misterobotique/ZTH11-Zigbee-Temperature-Humidity-Sensor/Schematic/ZTH11-ZTU_V1.2.kicad_sch

## KiCad design Schematic/ZTH11-ZTU_V1.2.kicad_sch (2026-03-07)

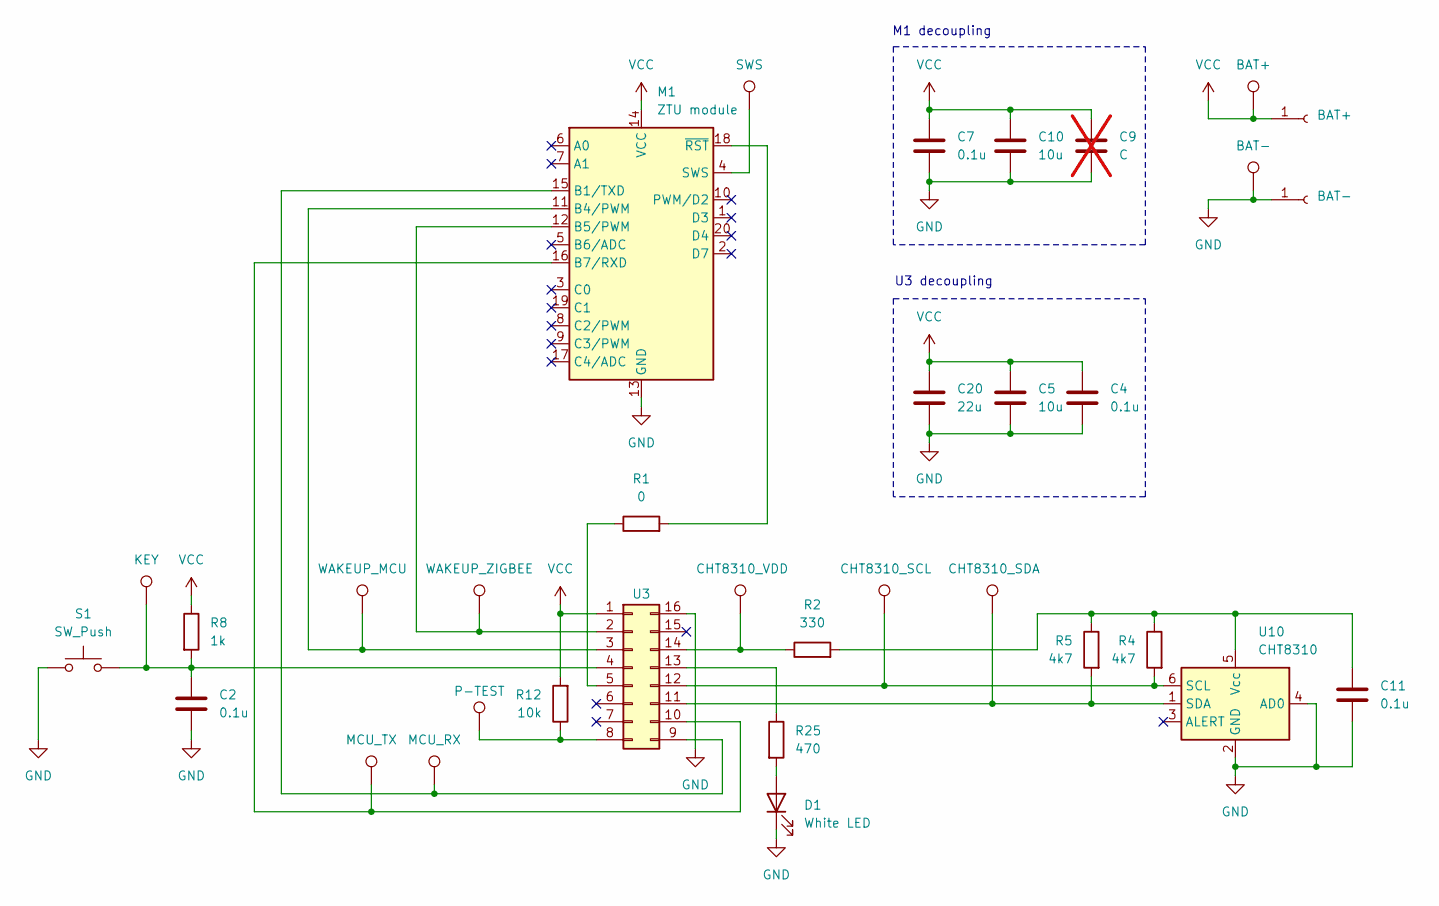
[picture p8: schematic ZTH11-ZTU_V1.2.kicad_sch]

Parts:
BAT+: TestPoint
BAT-: Conn_01x01_Socket
C2, C4, C7, C11: 0.1u
C5, C10: 10u
C9: C; not fitted
C20: 22u
CHT8310_SCL, CHT8310_SDA, CHT8310_VDD: TestPoint
D1: White LED
KEY: TestPoint
M1: ZTU module
MCU_RX: TestPoint
MCU_TX: TestPoint
P-TEST: TestPoint
R1: 0
R2: 330
R4, R5: 4k7
R8: 1k
R12: 10k
R25: 470
S1: SW_Push
SWS: TestPoint
U3: Conn_02x08_Counter_Clockwise
U10: CHT8310
WAKEUP_MCU: TestPoint
WAKEUP_ZIGBEE: TestPoint

Connections:
GND: BAT-.1, C2.2, C4.2, C5.2, C7.2, C9.2, C10.2, C11.2, C20.2, D1.1 (K), M1.13 (GND), S1.1, U3.16, U10.2 (GND), U10.4 (AD0)
unnamed: C2.1, KEY.1, R8.2, S1.2, U3.4
unnamed: C11.1, R2.2, R4.1, R5.1, U10.5 (Vcc)
unnamed: CHT8310_SCL.1, R4.2, U3.12, U10.6 (SCL)
unnamed: CHT8310_SDA.1, R5.2, U3.11, U10.1 (SDA)
unnamed: CHT8310_VDD.1, R2.1, U3.14
unnamed: D1.2 (A), R25.2
unnamed: M1.4 (SWS), SWS.1
unnamed: M1.11 (B4/PWM), U3.3, WAKEUP_MCU.1
unnamed: M1.12 (B5/PWM), U3.2, WAKEUP_ZIGBEE.1
unnamed: M1.15 (B1/TXD), MCU_RX.1, U3.9
unnamed: M1.16 (B7/RXD), MCU_TX.1, U3.10
unnamed: M1.18 (~RST), R1.2
unnamed: P-TEST.1, R12.1, U3.8
unnamed: R1.1, U3.5
unnamed: R25.1, U3.13
VCC: BAT+.1, C4.1, C5.1, C7.1, C9.1, C10.1, C20.1, M1.14 (VCC), R8.1, R12.2, U3.1

Notes on the sheet:
M1 decoupling
U3 decoupling
