misterobotique/ZTH11-Zigbee-Temperature-Humidity-Sensor/Measurements/data_sending(log_scale).png

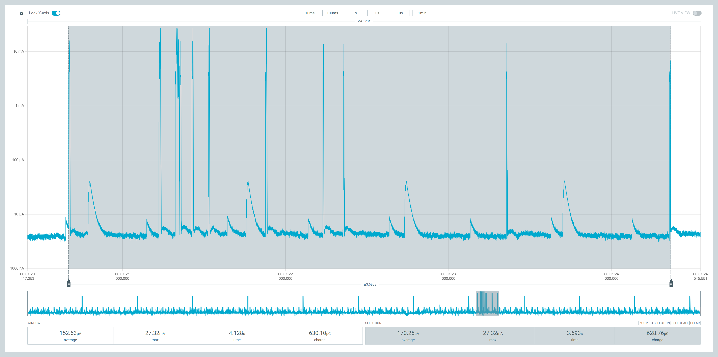
Measurements/data_sending(log_scale).png
